michael0093/Isolated-Diff-Probe/Detail of rev A2 mods.jpg

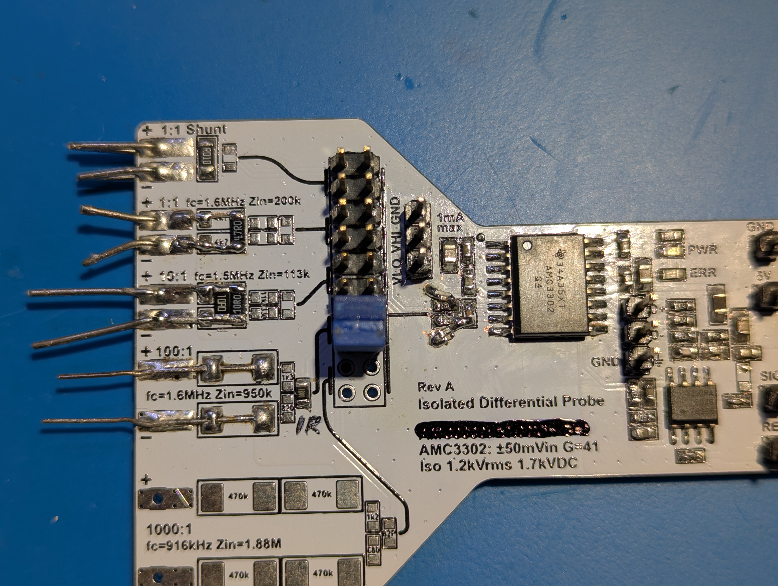
Detail of rev A2 mods.jpg
