michael0093/Isolated-Diff-Probe/Testing/20250809_204619_Bode AMC3302 1R.csv

Time | Milliseconds | Index | Freq | Vin | Vout | dB | Phase
2025-08-09 20:46:20.548333 | 1482 | 0 | 100 | 0.04400339 | 1.653493 | 31.498324501426765 | 1.8
2025-08-09 20:46:22.008273 | 2942 | 1 | 105.0 | 0.04333482 | 1.628242 | 31.497639121405623 | 1.894737
2025-08-09 20:46:23.445994 | 4380 | 2 | 110.25 | 0.04408919 | 1.657276 | 31.50125442039732 | 2.0
2025-08-09 20:46:24.862982 | 5797 | 3 | 115.76 | 0.04396782 | 1.647225 | 31.472359837545895 | 2.093023
2025-08-09 20:46:26.260456 | 7194 | 4 | 121.55 | 0.04318835 | 1.622887 | 31.498433382694046 | 2.195122
2025-08-09 20:46:27.643667 | 8578 | 5 | 127.63 | 0.04390895 | 1.649413 | 31.49552722560064 | 2.307692
2025-08-09 20:46:29.004110 | 9938 | 6 | 134.01 | 0.04346866 | 1.633333 | 31.4979696838476 | 2.4
2025-08-09 20:46:30.347852 | 11282 | 7 | 140.71 | 0.04323036 | 1.623887 | 31.49533905919491 | 2.535211
2025-08-09 20:46:31.675030 | 12609 | 8 | 147.75 | 0.04372878 | 1.642475 | 31.494628137804632 | 2.647059
2025-08-09 20:46:32.986889 | 13921 | 9 | 155.14 | 0.04299682 | 1.613481 | 31.4865503762605 | 2.8125
2025-08-09 20:46:34.284183 | 15218 | 10 | 162.9 | 0.04366705 | 1.639768 | 31.49257106986429 | 2.950819
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
