michael0093/Isolated-Diff-Probe/Testing/AMC3300 1-1, 1kHz 2V sine, Ch1=Vin,Ch2=Vout.png

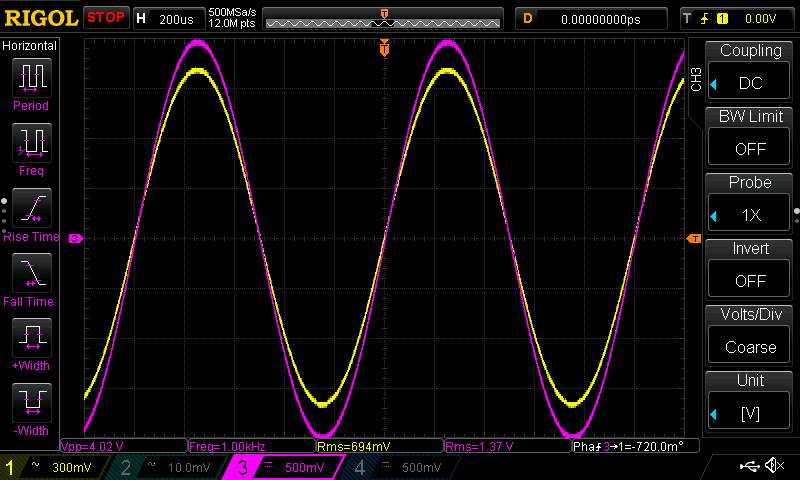
Testing/AMC3300 1-1, 1kHz 2V sine, Ch1=Vin,Ch2=Vout.png
