michael0093/Isolated-Diff-Probe/Testing/AMC3300 1-1, 100kHz 50mV sine, Ch1=Vin,Ch2=Vout.png

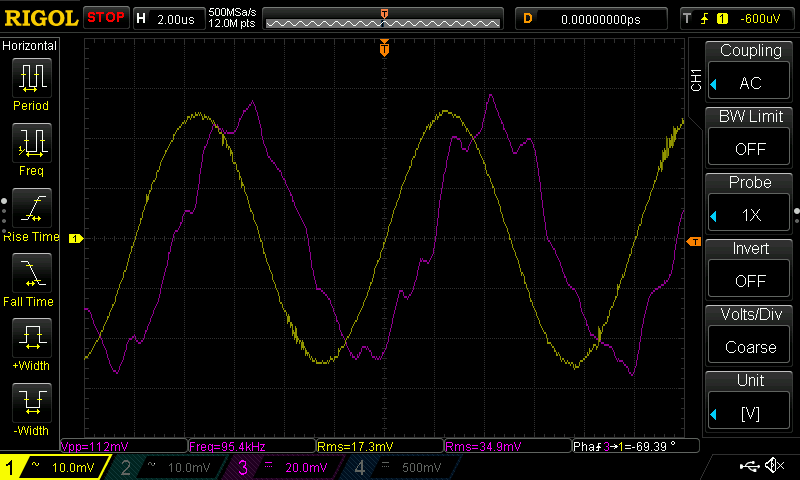
Testing/AMC3300 1-1, 100kHz 50mV sine, Ch1=Vin,Ch2=Vout.png
