michael0093/Isolated-Diff-Probe/Testing/AMC3300 10-1 frequency response.png

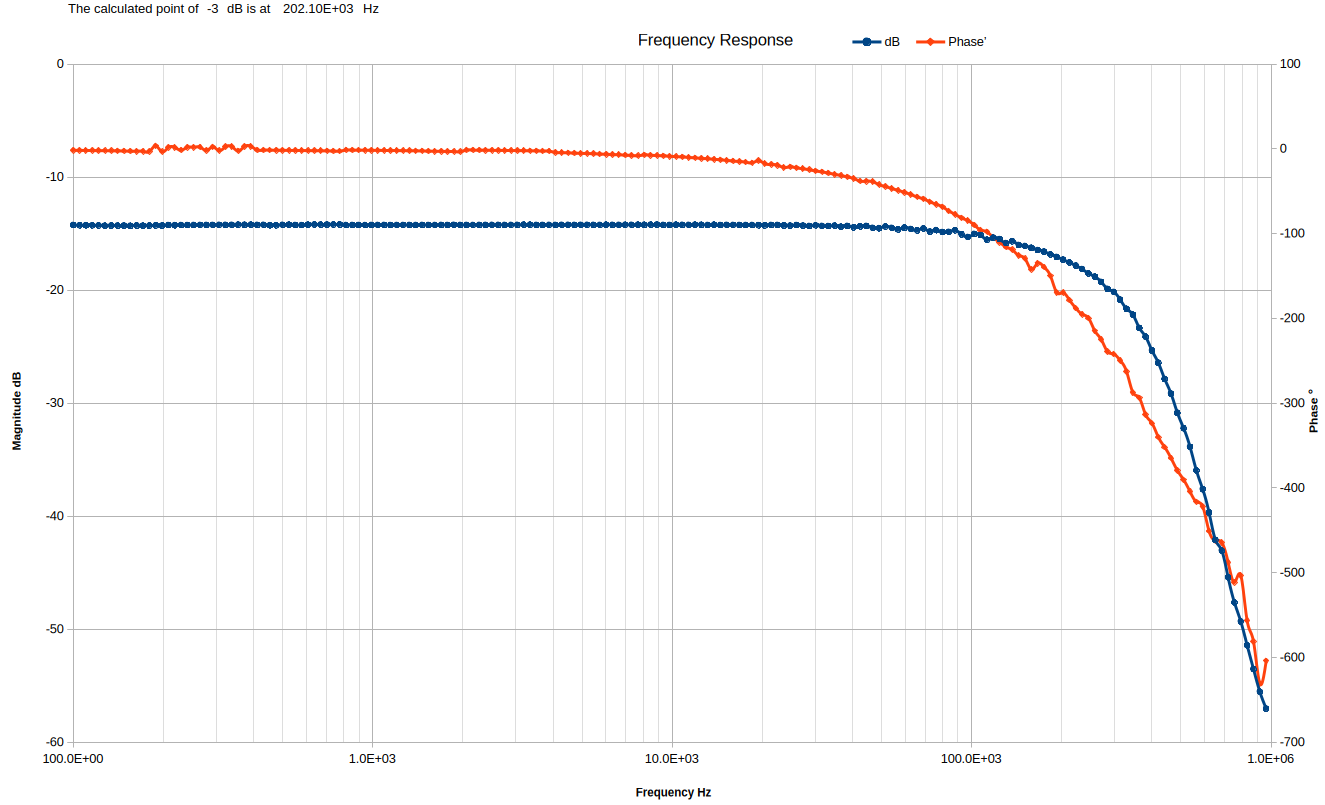
Testing/AMC3300 10-1 frequency response.png
