michael0093/Isolated-Diff-Probe/Testing/AMC3300 10-1 noise.png

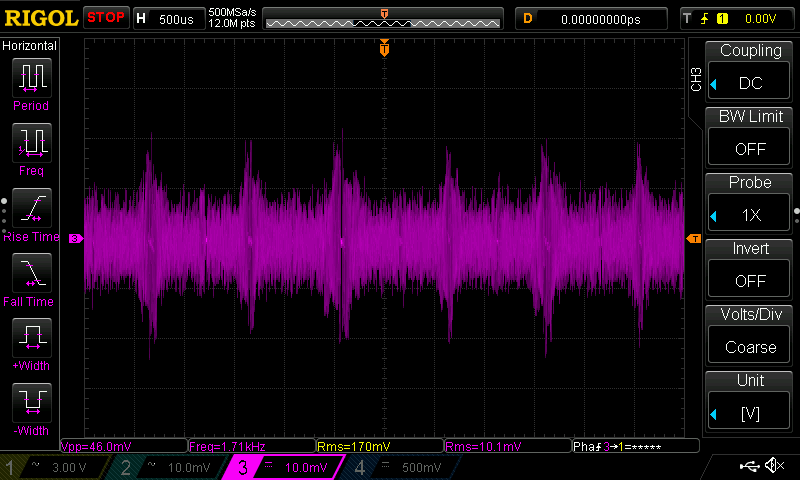
Testing/AMC3300 10-1 noise.png
