michael0093/Isolated-Diff-Probe/Testing/AMC3300 10-1, 200kHz sine, Ch1=Vin,Ch2=Vout.png

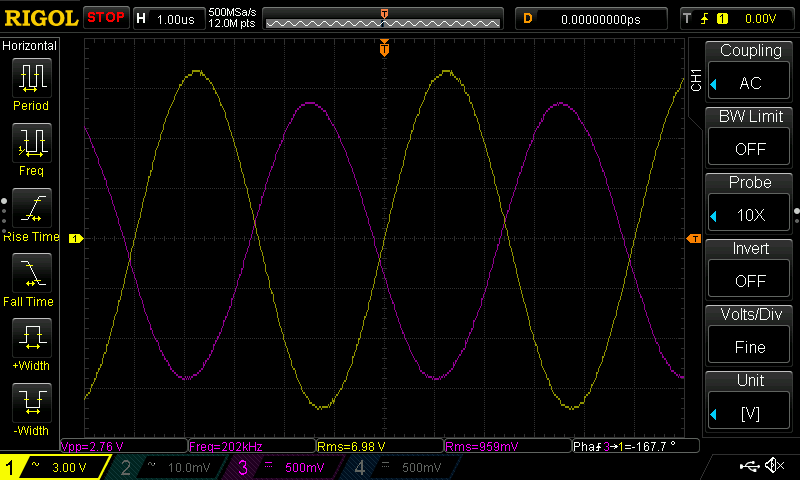
Testing/AMC3300 10-1, 200kHz sine, Ch1=Vin,Ch2=Vout.png
