michael0093/Isolated-Diff-Probe/Testing/AMC3300 10-1, 300kHz sine, Ch1=Vin,Ch2=Vout.png

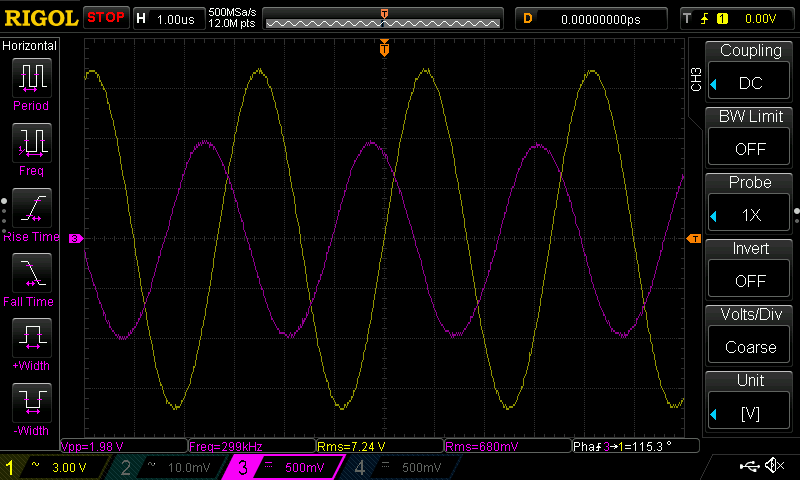
Testing/AMC3300 10-1, 300kHz sine, Ch1=Vin,Ch2=Vout.png
