michael0093/Isolated-Diff-Probe/Testing/AMC3302 0R01 noise.png

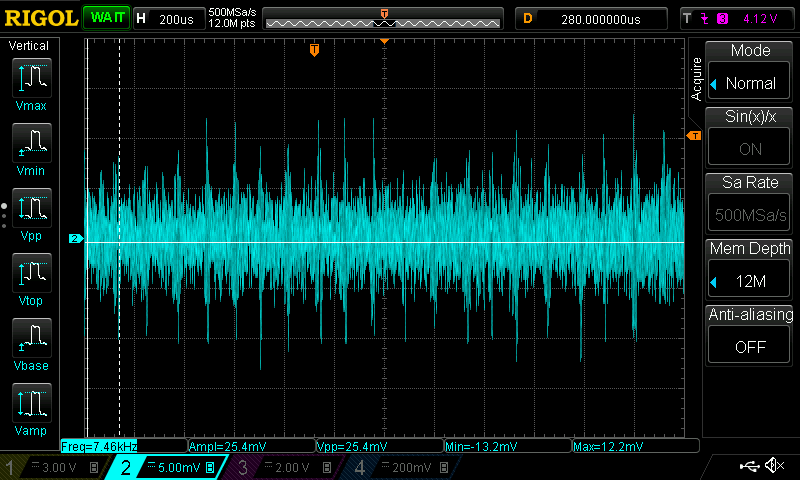
Testing/AMC3302 0R01 noise.png
