michael0093/Isolated-Diff-Probe/Testing/AMC3302 1R shunt noise.png

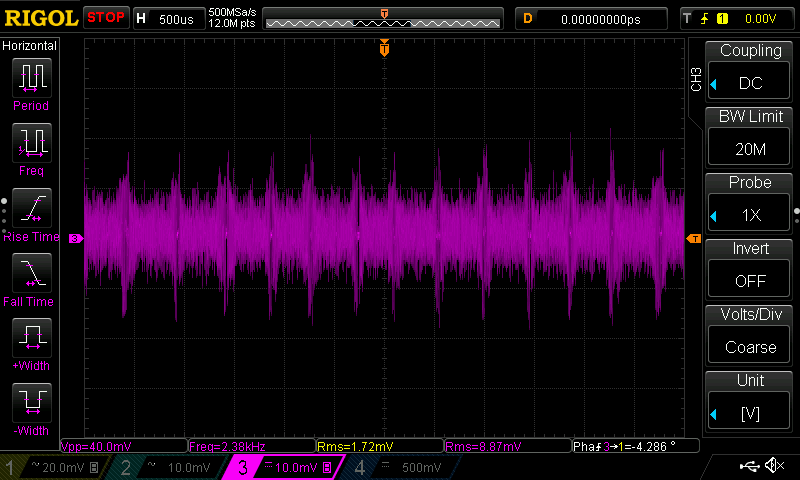
Testing/AMC3302 1R shunt noise.png
