michael0093/Isolated-Diff-Probe/Testing/AMC3302 1R shunt, 50kHz sine, Ch1=Vin,Ch2=Vout.png

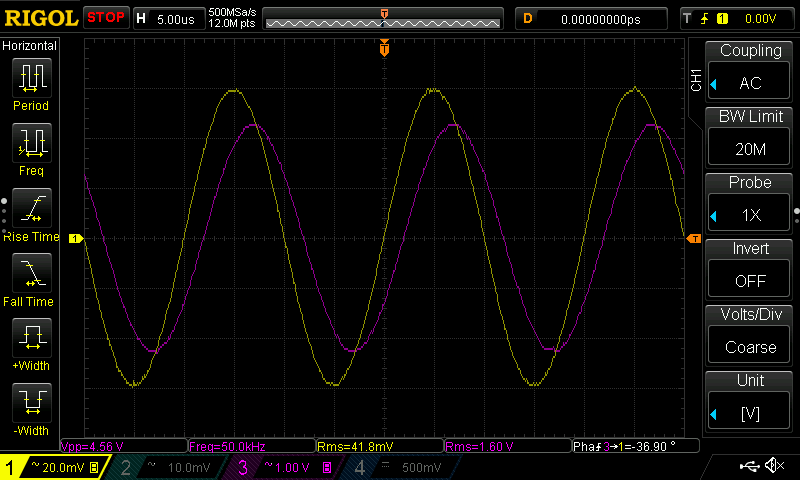
Testing/AMC3302 1R shunt, 50kHz sine, Ch1=Vin,Ch2=Vout.png
