michael0093/Isolated-Diff-Probe/Testing/AMC3302 100mA on 0R01 100kHz.png

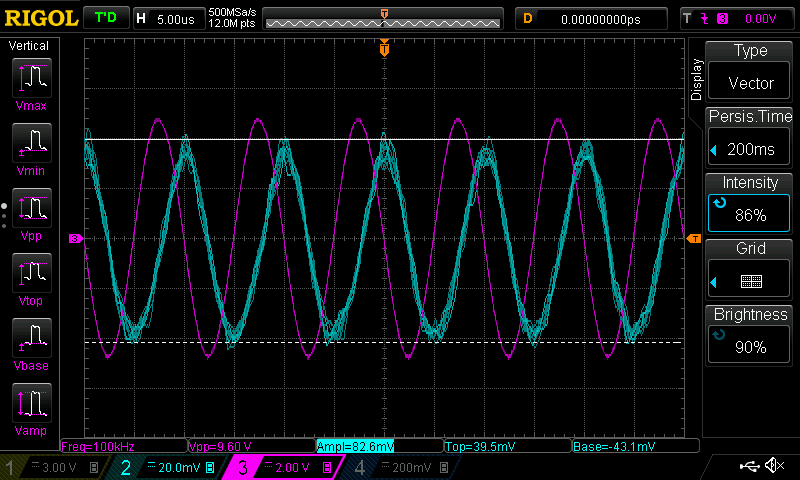
Testing/AMC3302 100mA on 0R01 100kHz.png
