michael0093/Isolated-Diff-Probe/Testing/AMC3302 100mA on 0R01 avg.png

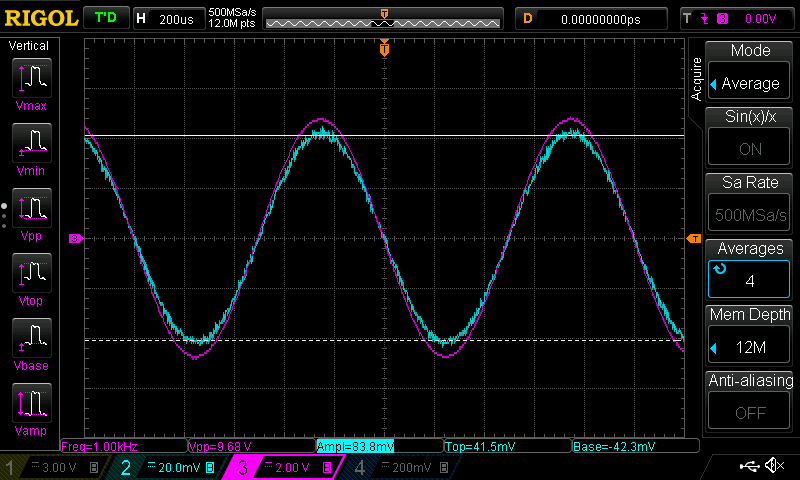
Testing/AMC3302 100mA on 0R01 avg.png
