michael0093/Isolated-Diff-Probe/Testing/AMC3302 100mA on 0R01 Square 3.png

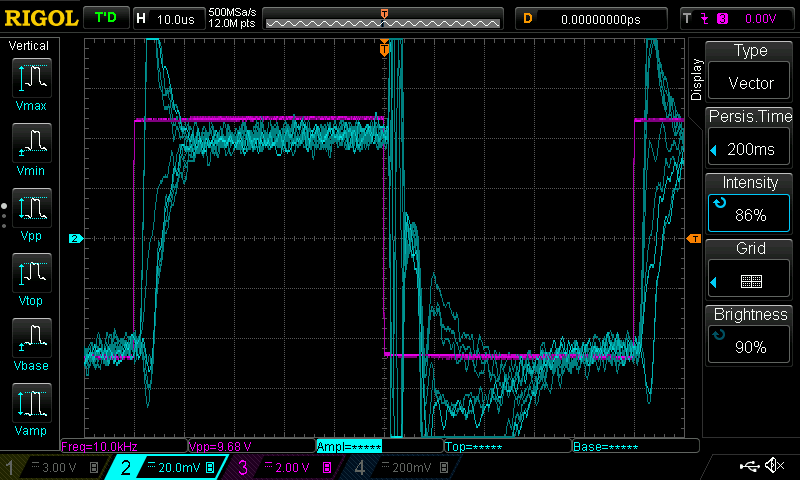
Testing/AMC3302 100mA on 0R01 Square 3.png
