michael0093/Isolated-Diff-Probe/Testing/AMC3302 shorted noise.png

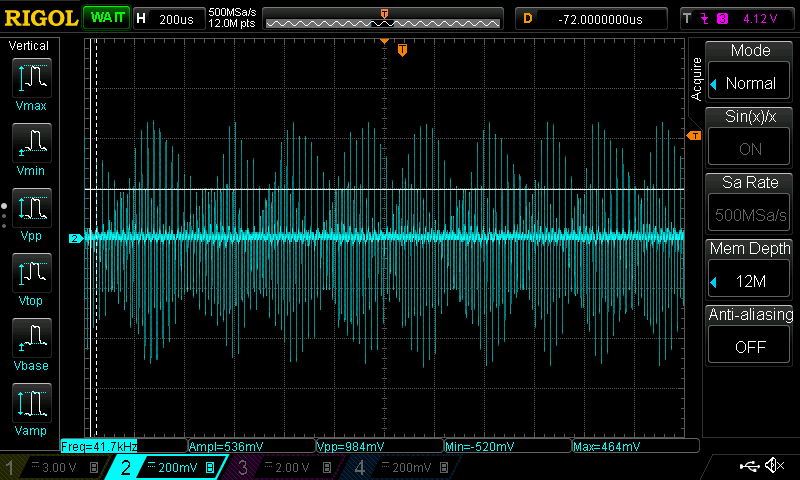
Testing/AMC3302 shorted noise.png
