michael0093/Isolated-Diff-Probe/Testing/AMC3330 1V 330kHz.png

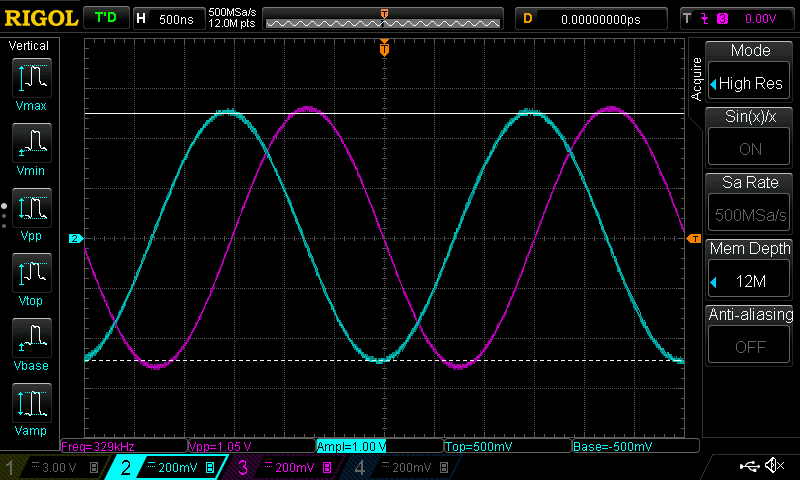
Testing/AMC3330 1V 330kHz.png
