michael0093/Isolated-Diff-Probe/Testing/AMC3330 1V.png

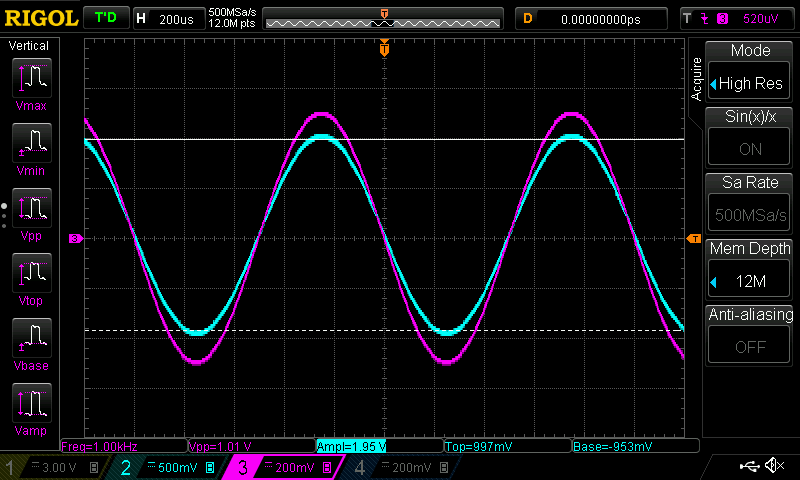
Testing/AMC3330 1V.png
