michael0093/Isolated-Diff-Probe/Testing/AMC3330 10mV.png

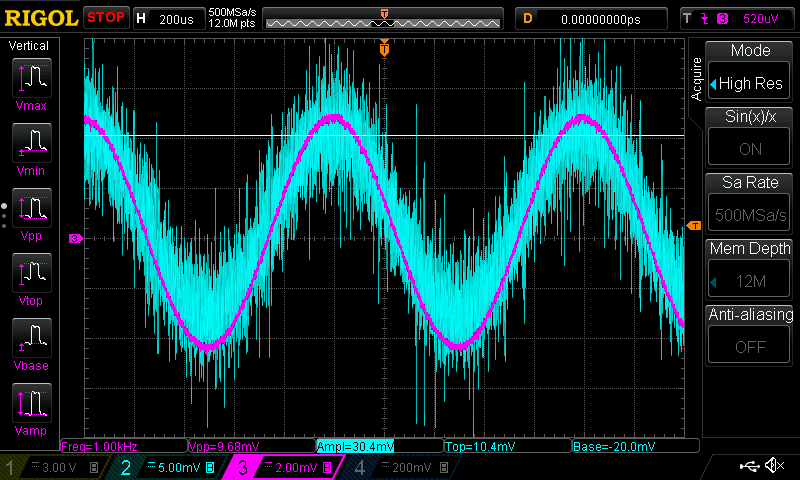
Testing/AMC3330 10mV.png
