michael0093/Isolated-Diff-Probe/Testing/AMC3330 70mV 110kHz Square.png

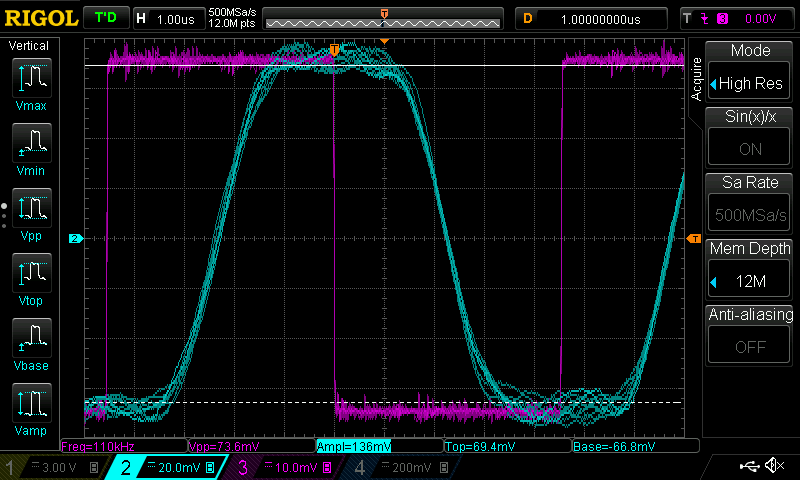
Testing/AMC3330 70mV 110kHz Square.png
