michael0093/Isolated-Diff-Probe/Testing/AMC3330  1V 1kHz Square.png

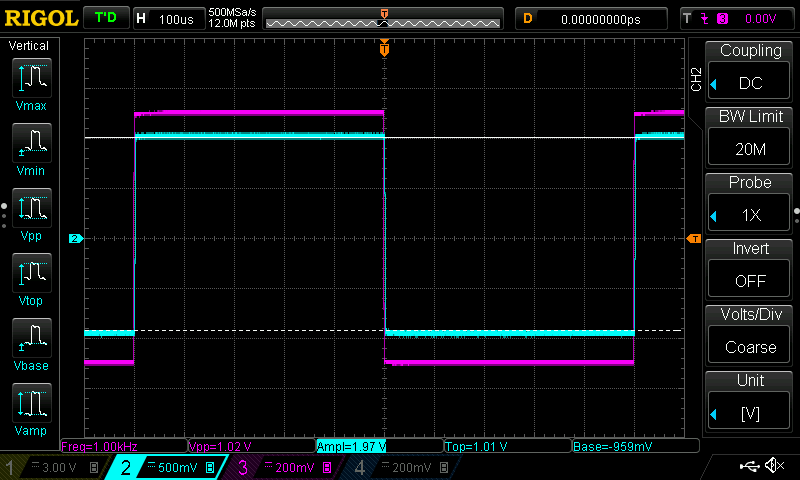
Testing/AMC3330 1V 1kHz Square.png
