michael0093/Isolated-Diff-Probe/Testing/AMC3330  1V 110kHz Square.png

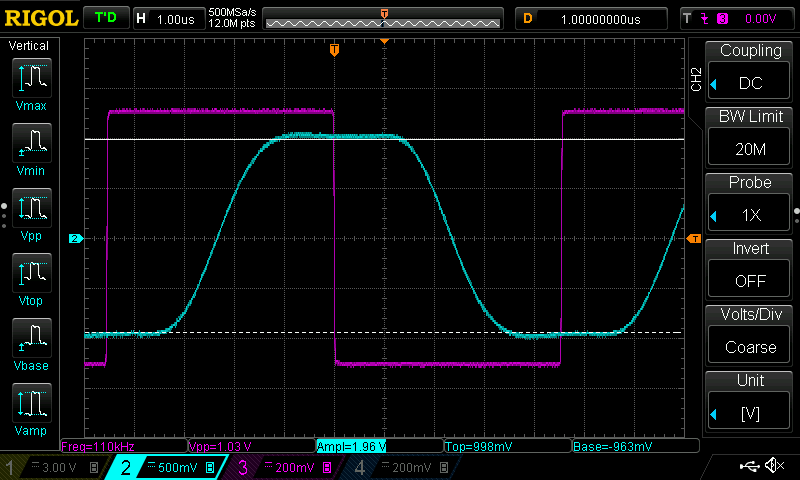
Testing/AMC3330 1V 110kHz Square.png
