michael0093/Isolated-Diff-Probe/Testing/AMC3330 short cct noise.png

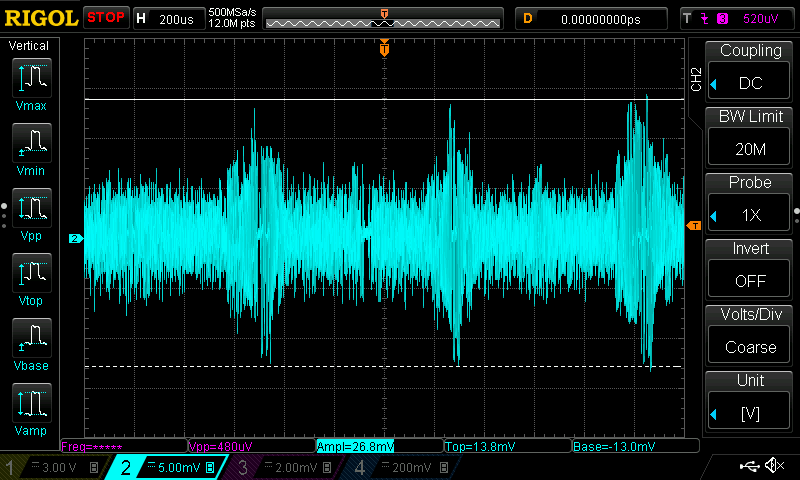
Testing/AMC3330 short cct noise.png
