michael0093/Isolated-Diff-Probe/Input Divider.asc

C1: cap; 33p
C2: cap; 100p
C3: cap; 33p
C4: cap; 33p
C5: cap; 33p
C6: cap; 33p
C7: cap; 33p
C8: cap; 33p
C9: cap; 33p
C10: cap; 33p
C11: cap; 33p
C12: cap; 33p
C13: cap; 33p
C14: cap; 3n3
C15: cap; 3n3
C16: cap; 3n3
C17: cap; 33p
C18: cap; 33p
C19: cap; 33p
C20: cap; 100n
R1: res; 470k
R2: res; 470k
R3: res; 470k
R4: res; 470k
R5: res; 1k2
R6: res; 22
R7: res; 22
R8: res; 470k
R9: res; 8k2
R10: res; 1k3
R11: res; 470k
R12: res; 680
R13: res; 22
R14: res; 22
R15: res; 51k
R16: res; 11k
R17: res; 330
R18: res; 51k
R19: res; 22
R20: res; 22
R21: res; 4k7
R22: res; 22
R23: res; 1
R24: res; 4k7
R25: res; 22
R26: res; 100k
R27: res; 22
R28: res; 22
R29: res; 100k
R30: res; 1Meg
R31: res; 1Meg
R32: res; 1Meg
R33: res; 1Meg
R34: res; 1Meg
R35: res; 1Meg
R36: res; 1Meg
R37: res; 1Meg
R38: res; 22
R39: res; 22
R40: res; 1
R41: res; 100k
R42: res; 100k
R43: res; 1k
R44: res; 1k
V1: voltage; ""; AC 1
Named nets: 0, Vin1000+, Vin1000-, Vin100+, Vin100-, Vin10+, Vin10-, Vin1+, Vin1-, Shunt2+, Shunt2-, Shunt+, Shunt-
.ac dec 100 1 10meg
1000:1 fc=560kHz
Zin = 1.88M
100:1 fc=340kHz
Zin = 950k
10:1 fc=315kHz
Zin = 113k
1:1 fc=338kHz
Zin = 200k
Shunt fc=730kHz
Zin = 1R
Shunt fc 730lHz
Zin = 1R
